DBXYD/2526_Projet1AB_Khess/Software/Caisse_enregistreuse-teste/Core/Inc/main.h

#define B1_Pin GPIO_PIN_13
#define B1_GPIO_Port GPIOC
#define USART_TX_Pin GPIO_PIN_2
#define USART_TX_GPIO_Port GPIOA
#define USART_RX_Pin GPIO_PIN_3
#define USART_RX_GPIO_Port GPIOA
#define green_Pin GPIO_PIN_5
#define green_GPIO_Port GPIOA
#define TMS_Pin GPIO_PIN_13
#define TMS_GPIO_Port GPIOA
#define TCK_Pin GPIO_PIN_14
#define TCK_GPIO_Port GPIOA
#define nCS_Pin GPIO_PIN_15
#define nCS_GPIO_Port GPIOA
