DBXYD/2526_Projet1AB_Khess/Software/Caisse_enregistreuse-teste/Core/Src/main.c

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
/* Includes ------------------------------------------------------------------*/
#include "main.h"
#include "spi.h"
#include "tim.h"
#include "usart.h"
#include "gpio.h"

/* USER CODE BEGIN Includes */
#include <stdint.h>
#include "pn532.h"
#include "stdio.h"
#include "string.h"
#include "pn532_stm32f1.h"
/* USER CODE END Includes */

/* USER CODE BEGIN PD */
#define use_HEXADECIMAL
/* USER CODE END PD */


/* USER CODE BEGIN PV */
PN532 pn532;

/* USER CODE END PV */

void SystemClock_Config(void);
/* USER CODE BEGIN 0 */
#ifdef __GNUC__
#define PUTCHAR_PROTOTYPE int __io_putchar(int ch)
#else
#define PUTCHAR_PROTOYPE int fputc(int ch, FILE *f)
#endif

PUTCHAR_PROTOTYPE
{
	HAL_UART_Transmit(&huart2, (uint8_t *)&ch, 1, HAL_MAX_DELAY);
	return ch;
}
/* USER CODE END 0 */

/**
  * @brief  The application entry point.
  * @retval int
  */
int main(void)
{

  /* USER CODE BEGIN 1 */


	uint8_t buff[255];
	uint8_t uid[MIFARE_UID_MAX_LENGTH];
	int32_t uid_len = 0;
  /* USER CODE END 1 */

  /* MCU Configuration--------------------------------------------------------*/

  /* Reset of all peripherals, Initializes the Flash interface and the Systick. */
  HAL_Init();

  /* Configure the system clock */
  SystemClock_Config();

  /* Initialize all configured peripherals */
  MX_GPIO_Init();
  MX_USART2_UART_Init();
  MX_TIM2_Init();
  MX_SPI2_Init();
  /* USER CODE BEGIN 2 */
//  void SPI_TransmitReceive(uint8_t dataToSend, uint8_t* receivedData)
//  {
//      HAL_GPIO_WritePin(GPIOA, GPIO_PIN_15, GPIO_PIN_RESET); // Activer le PN532 (mettre SS à LOW)
//
//      HAL_SPI_Transmit(&hspi2, &dataToSend, 1, HAL_MAX_DELAY); // Transmettre un octet
//
//      HAL_SPI_Receive(&hspi2, receivedData, 1, HAL_MAX_DELAY);  // Lire la réponse du PN532
//
//      HAL_GPIO_WritePin(GPIOA, GPIO_PIN_15, GPIO_PIN_SET); // Désactiver le PN532 (mettre SS à HIGH)
//  }


  /* USER CODE END 2 */

  /* Infinite loop */
  /* USER CODE BEGIN WHILE */
  while (1)
  {
	  /*HAL_GPIO_WritePin(GPIOC, GPIO_PIN_9, 1);
	  HAL_GPIO_WritePin(GPIOC, GPIO_PIN_8, 1);
	  HAL_GPIO_WritePin(GPIOB, GPIO_PIN_15, 1);
	  HAL_GPIO_WritePin(GPIOB, GPIO_PIN_14, 1);
	  if(flag==1){
		  HAL_GPIO_TogglePin(green_GPIO_Port, green_Pin);
		  flag=0;*/
	   uint8_t testByte[10] = {0xAA, 0x10, 0x20, 0xAA, 0x10, 0x20, 0xAA, 0x10, 0x20, 0xAA}; // Octet à envoyer
	   uint8_t receivedByte = 0;

	    // Envoi et réception via SPI
//	    SPI_TransmitReceive(testByte, &receivedByte);

	    // Vérifier la réponse
	    printf("Octet envoyé: 0x%02X, Octet reçu: 0x%02X\r\n", testByte, receivedByte);

	    if (HAL_GPIO_ReadPin(GPIOC, GPIO_PIN_10) == GPIO_PIN_RESET) {
	        printf("IRQ est à LOW : le PN532 a une donnée prête.\r\n");
	    } else {
	        printf("IRQ est à HIGH : le PN532 ne signale rien.\r\n");
	    }

	    HAL_Delay(1000); // Petite pause pour éviter de surcharger le terminal

	    HAL_GPIO_WritePin(nCS_GPIO_Port, nCS_Pin, RESET);
	    HAL_SPI_Transmit(&hspi2, testByte, 10, 100);
	    HAL_GPIO_WritePin(nCS_GPIO_Port, nCS_Pin, SET);
    /* USER CODE END WHILE */

    /* USER CODE BEGIN 3 */



  }
  /* USER CODE END 3 */
}

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
/* USER CODE BEGIN 4 */
void HAL_GPIO_EXTI_Callback(uint16_t GPIO_Pin){
	//flag=1;
}
/* USER CODE END 4 */
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
